blurbler2/TL082CP/kicad/guitar-pedal.jpeg

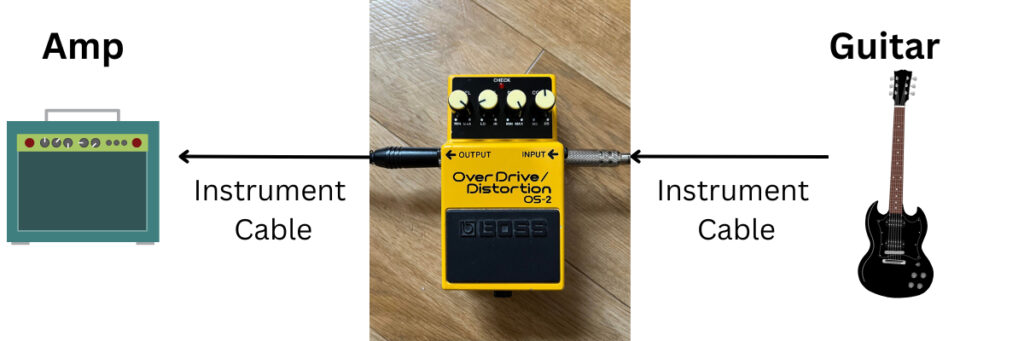
kicad/guitar-pedal.jpeg
