blurbler2/TL082CP/kicad/NEUTRIKJKS/NEUTRIKJKS.jpg

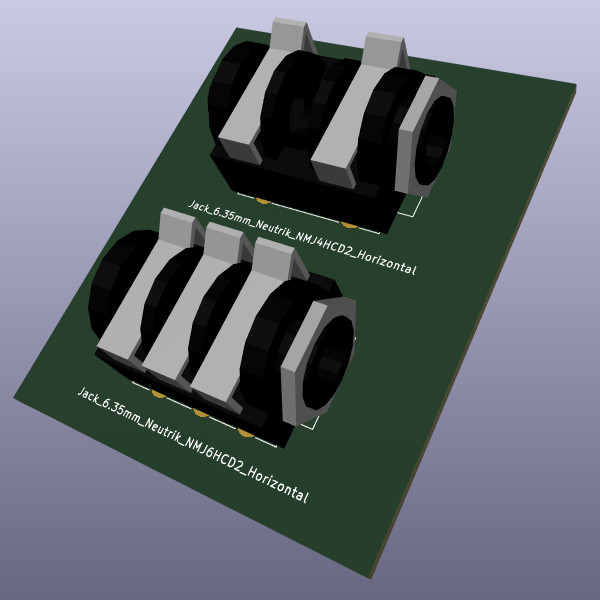
kicad/NEUTRIKJKS/NEUTRIKJKS.jpg
