blurbler2/TL082CP/ltspice/ltspice-simulation-1-buffer-slew-rate/plot.png

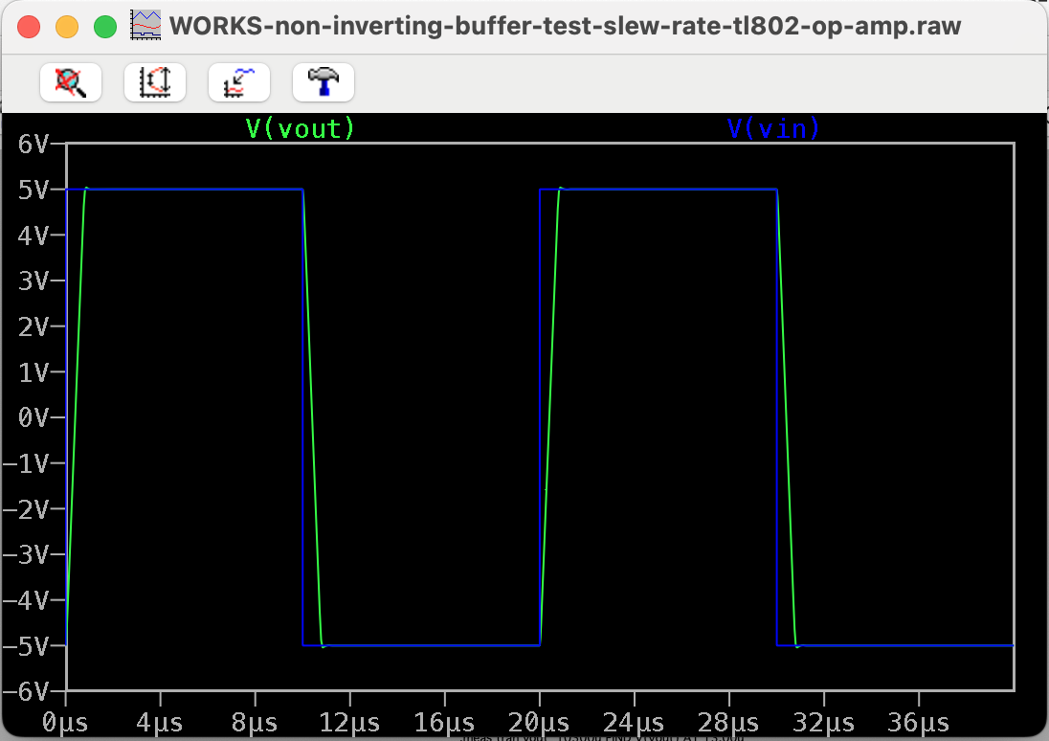
ltspice/ltspice-simulation-1-buffer-slew-rate/plot.png
