blurbler2/TL082CP/ltspice/ltspice-simulation-1-comparator-slew-rate/errorlog.png

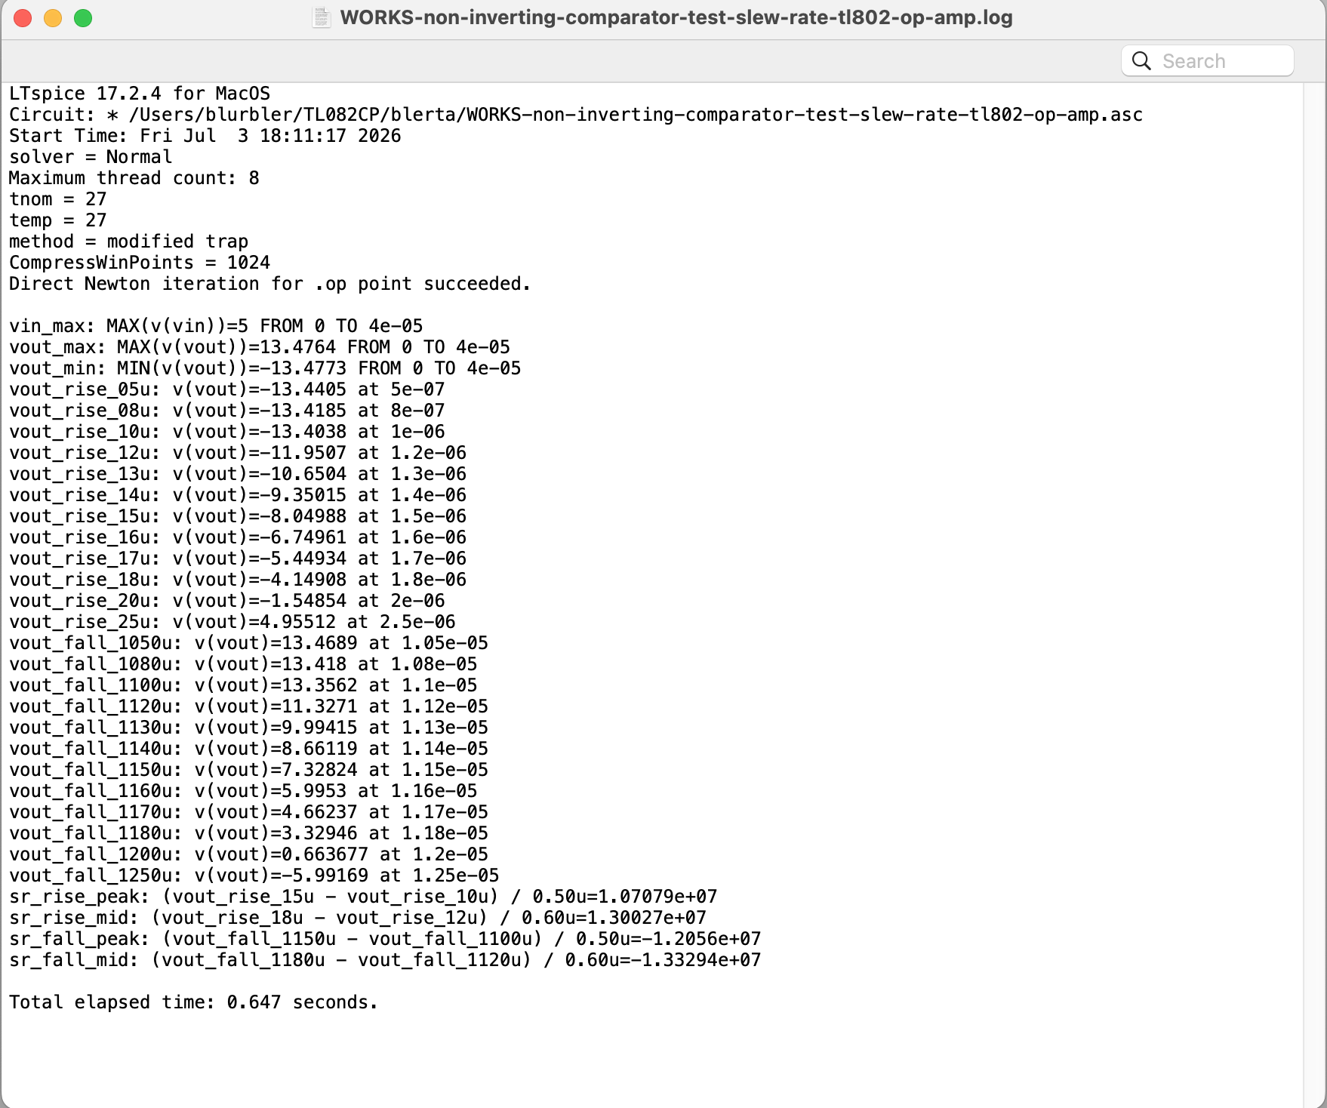
ltspice/ltspice-simulation-1-comparator-slew-rate/errorlog.png
