blurbler2/TL082CP/mechanisch/TL082CP-NOPB_2to1.png

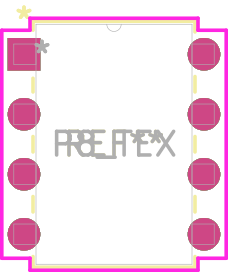
mechanisch/TL082CP-NOPB_2to1.png
