blurbler2/TL082CP/mechanisch/TL082CP_PCB_1to1.png

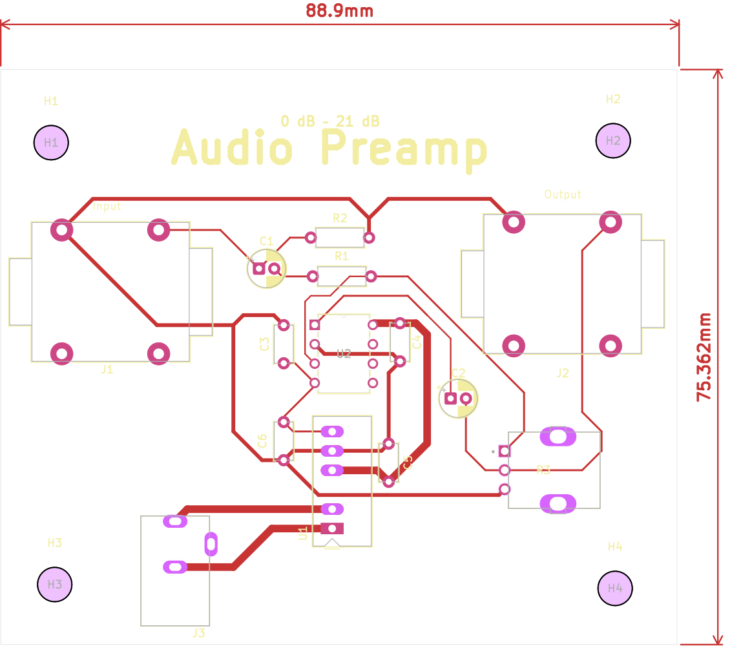
mechanisch/TL082CP_PCB_1to1.png
