blurbler2/TL082CP/mechanisch/Traegerplatte_1zu1.png

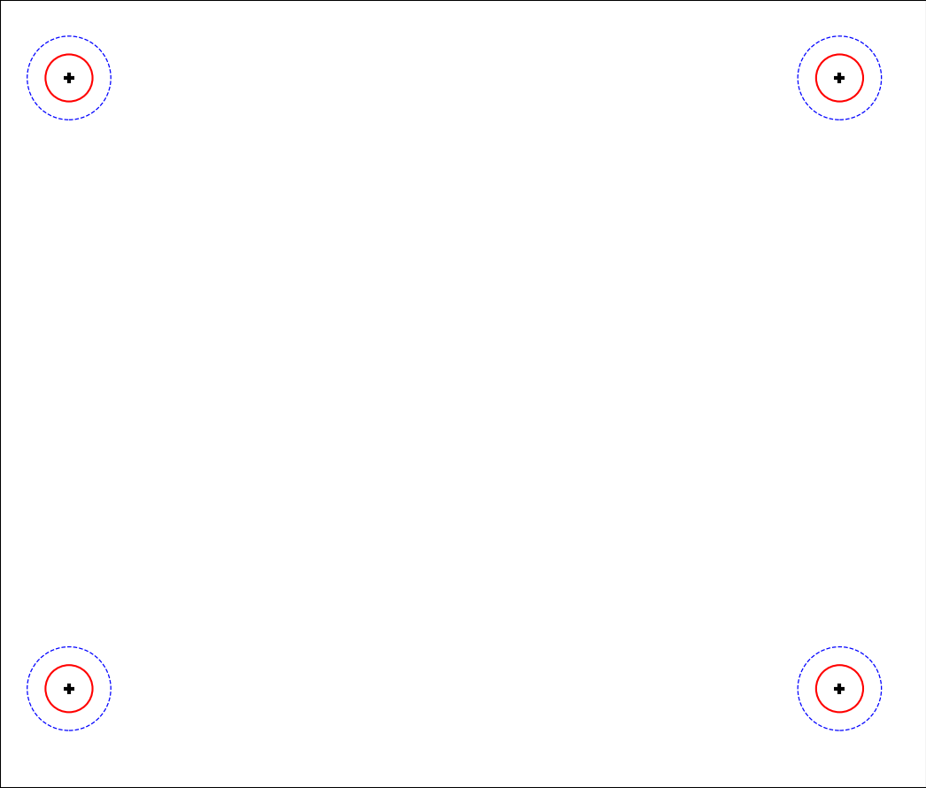
mechanisch/Traegerplatte_1zu1.png
