blurbler2/TL082CP/kicad/TL082CP/plots/TL082CP.pdf

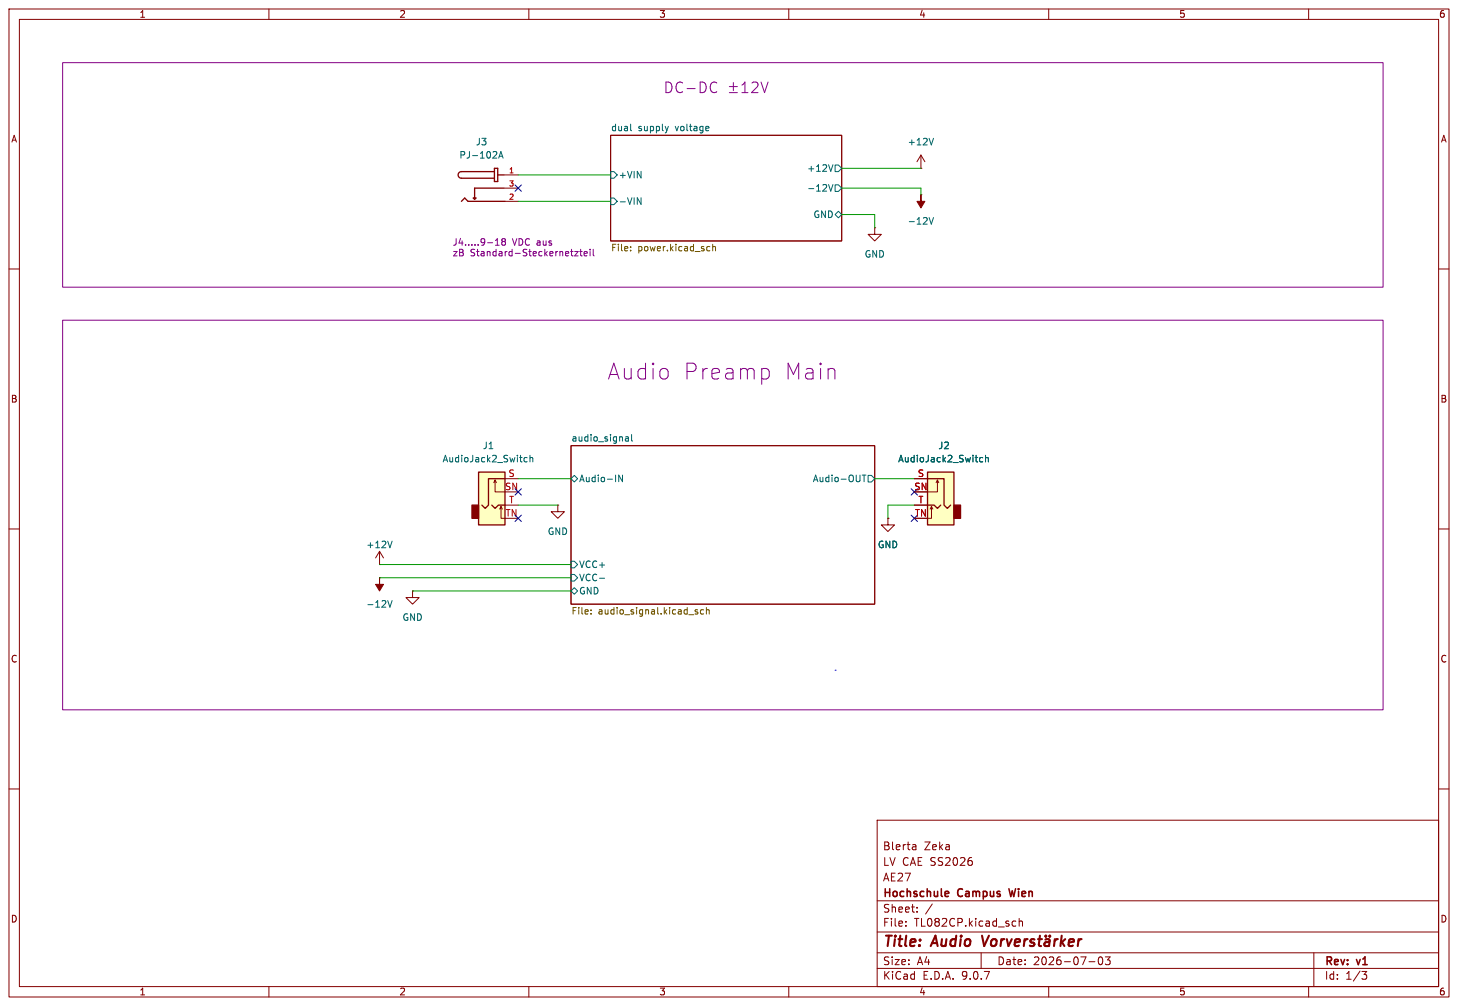
[picture p32: page 1]

LV CAE SS2026 Blerta Zeka

Id: 1/3 Title: Audio þÿVorverstärker File: TL082CP.kicad_sch Sheet: / Hochschule Campus Wien AE27

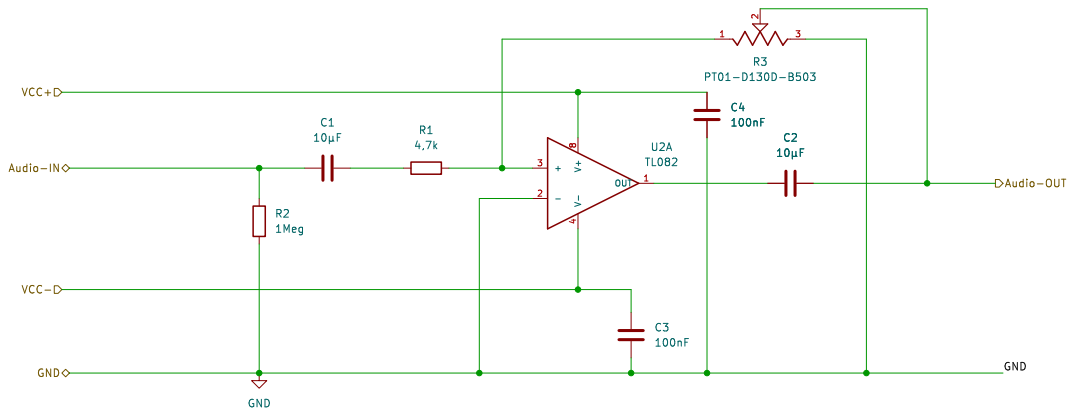
[picture p33: page 2]

Id: 3/3 Title: File: audio_signal.kicad_sch Sheet: /audio_signal/

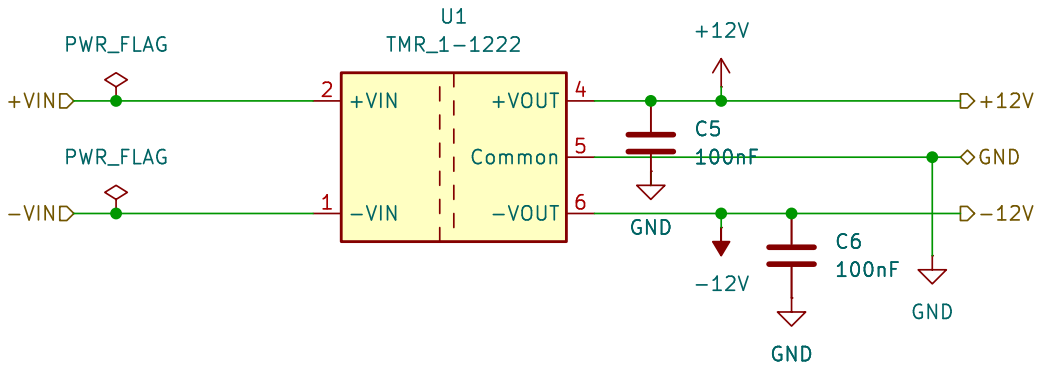
[picture p34: page 3]
